adafruit/Adafruit_MagTag_PCBs/assets/4800.jpg

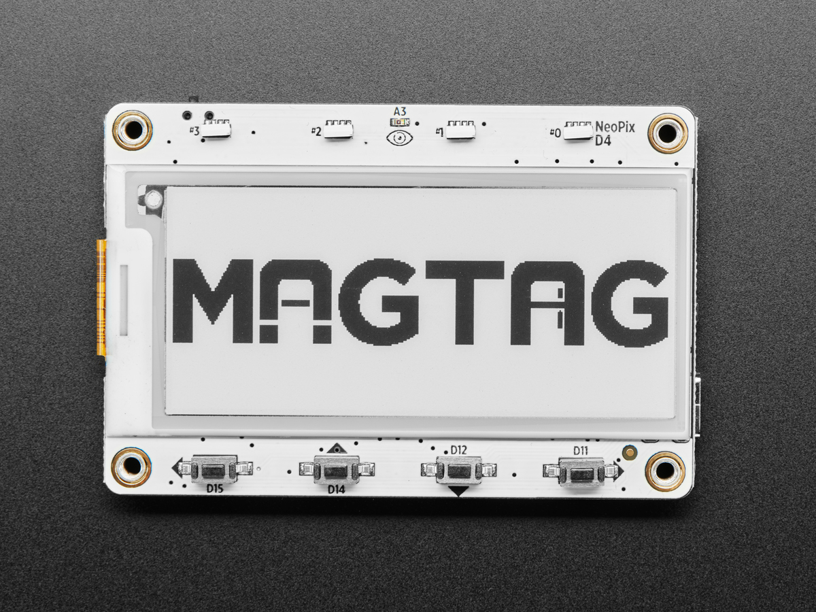
assets/4800.jpg
